vovets/led_lamp/fw/deep_sleeper/event_list.h

#pragma once

struct Event;

void tmHandleAlarm(struct Event* e);
void handlePinChange(struct Event* e);

#define EVENT_LIST                                                     \
X(alarm,     Alarm,     1, EL_EMPTY,        tmHandleAlarm,   SEP)      \
X(pinChange, PinChange, 2, EL_EMPTY,        handlePinChange, SEP)
